RAKWireless/RAK10706-Signal-Meter/SignalMeterTool/assets/11-menu-info.png

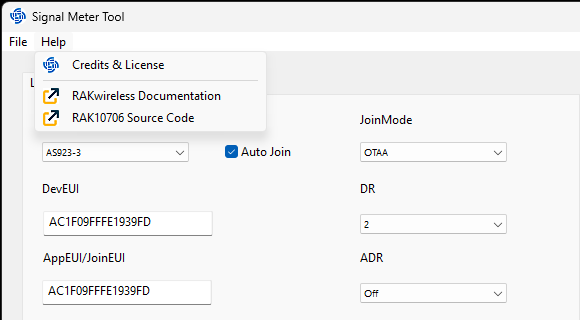
SignalMeterTool/assets/11-menu-info.png
