RAKWireless/RAK10706-Signal-Meter/sd-card.cpp

/**
 * @file sd-card.cpp
 * @author Bernd Giesecke (bernd@giesecke.tk)
 * @brief SD card functions
 * @version 0.2
 * @date 2024-11-18
 *
 * @copyright Copyright (c) 2024
 *
 */
#include "app.h"
#include <SD.h> //http://librarymanager/All#SD

/** Forward declarations */
void dir_sd(File dir);
void dump_sd_file(const char *path);

/** Pointer to current log file */
File log_file;

/** Flag if write or file create failed */
volatile bool sd_card_error = false;

/** Number of lines written to file */
volatile uint16_t lines_written = 0;

/**
 * @brief Initialize SD card
 *
 * @return true SD card found
 * @return false no SD card found
 */
bool init_sd(void)
{
	digitalWrite(WB_IO2, HIGH);
	delay(50);

#if 0
	// For debug, get more info about SD card
	Sd2Card card;
	SdVolume volume;

	if (!card.init(SPI_QUARTER_SPEED, WB_SPI_CS)) // SPI_QUARTER_SPEED SPI_HALF_SPEED SPI_FULL_SPEED
	{
		MYLOG("SD", "Card Init Failed! Please make sure the card is inserted!");
		return false;
	}

	switch (card.type())
	{
	case SD_CARD_TYPE_SD1:
		MYLOG("SD", "Cardtype SD1");
		break;
	case SD_CARD_TYPE_SD2:
		MYLOG("SD", "Cardtype SD2");
		break;
	case SD_CARD_TYPE_SDHC:
		MYLOG("SD", "Cardtype SDHC");
		break;
	default:
		MYLOG("SD", "Cardtype inknown");
	}

	if (!volume.init(card))
	{
		MYLOG("SD", "Could not find FAT16/FAT32 partition.\nMake sure you've formatted the card");
		return false;
	}

	MYLOG("SD", "Clusters: %ld", volume.clusterCount());
	MYLOG("SD", "Blocks x Cluster: %d", volume.blocksPerCluster());

	MYLOG("SD", "Total Blocks: %ld", volume.blocksPerCluster() * volume.clusterCount());

	// print the type and size of the first FAT-type volume
	uint32_t volumesize;
	MYLOG("SD", "Volume type is:    FAT%d", volume.fatType(), DEC);

	volumesize = volume.blocksPerCluster(); // clusters are collections of blocks
	volumesize *= volume.clusterCount();	// we'll have a lot of clusters
	volumesize /= 2;						// SD card blocks are always 512 bytes (2 blocks are 1 KB)
	MYLOG("SD", "Volume size (KB): %ld", volumesize);
	MYLOG("SD", "Volume size (MB): %ld", volumesize / 1024);
	MYLOG("SD", "Volume size (GB): %.2f", (float)volumesize / 1024 / 1024.0);
#endif

	if (!SD.begin(WB_SPI_CS))
	{
		MYLOG("SD", "SD begin failed.\nMake sure you've formatted the card and it is inserted");
		return false;
	}

#if 0
	// For debug, list available files
	File dir_file = SD.open("/", FILE_WRITE);
	dir_sd(dir_file);
	dir_file.close();

	uint16_t file_num = 0;
	sprintf((char *)file_name, "%04d-log.csv", file_num);
	while (true)
	{
		if (SD.exists((const char *)file_name))
		{
			MYLOG("SD", "Content of %s:", file_name);
			dump_sd_file((const char *)file_name);
			file_num++;
			sprintf((char *)file_name, "%04d-log.csv", file_num);
		}
		else
		{
			break;
		}
	}
#endif

	SD.end();
	return true;
}

#if 0
/**
 * @brief Send directory of a folder to the Serial port
 *
 * @param dir
 */
void dir_sd(File dir)
{
	digitalWrite(WB_IO2, HIGH);
	delay(50);
	while (true)
	{

		log_file = dir.openNextFile();
		if (!log_file)
		{
			// no more files
			break;
		}
		Serial.print(log_file.name());
		if (log_file.isDirectory())
		{
			Serial.println("/");
			dir_sd(log_file);
		}
		else
		{
			// files have sizes, directories do not
			Serial.print("\t\t");
			Serial.println(log_file.size(), DEC);
		}
		log_file.close();
	}
}
#endif

/**
 * @brief Send content of all files to the Serial port
 *
 */
void dump_all_sd_files(void)
{
	SD.begin(WB_SPI_CS);
	uint16_t file_num = 0;
	sprintf((char *)file_name, "%04d-log.csv", file_num);
	while (true)
	{
		if (SD.exists((const char *)file_name))
		{
			// MYLOG("SD", "Content of %s:", file_name);
			// Serial.println("=====================================================");
			log_file = SD.open((const char *)file_name, FILE_READ); // re-open the file for reading.
			if (log_file)
			{
				oled_clear();
				oled_write_header("LOGGING", false);
				oled_add_line((char *)"Dumping SD card");
				oled_add_line((char *)"Do not power off");
				sprintf(line_str, "%s", file_name);
				oled_write_line(3, 0, line_str);
				oled_display();
				Serial.printf("%s\r\n", file_name);
				Serial.write(0x02);
				Serial.flush();
				// Delay to give receiver time to get filename
				delay(500);
				while (log_file.available())
				{
					Serial.write(log_file.read()); // read from the file until there's nothing else in it.
					delay(5);
				}
				log_file.close(); // close the file.
				Serial.flush();

				// Delay to give receiver time to get EOF marker
				delay(500);

				Serial.write(0x03);
				Serial.flush();

				// Delay to give receiver time to get EOF marker
				delay(500);
			}
			else
			{
				MYLOG("SD", "Failed to open file for reading."); // if the file didn't open, print an error.
			}

			file_num++;
			sprintf((char *)file_name, "%04d-log.csv", file_num);
			MYLOG("SD", "Look for next file %s", file_name);
		}
		else
		{
			Serial.write(0x17);
			Serial.flush();
			break;
		}
	}

	SD.end();
}

/**
 * @brief Send the content of a file to the Serial port
 *
 * @param path Path as string
 */
void dump_sd_file(const char *path)
{
	digitalWrite(WB_IO2, HIGH);
	delay(50);
	MYLOG("SD", "Reading file: %s", path);

	SD.begin(WB_SPI_CS);

	log_file = SD.open(path, FILE_READ); // re-open the file for reading.
	if (log_file)
	{
		while (log_file.available())
		{
			Serial.write(log_file.read()); // read from the file until there's nothing else in it.
			delay(5);
		}
		log_file.close(); // close the file.
	}
	else
	{
		MYLOG("SD", "Failed to open file for reading."); // if the file didn't open, print an error.
	}
	SD.end();
}

/**
 * @brief Erase all files on the SD card
 *
 */
void clear_sd_file(void)
{
	digitalWrite(WB_IO2, HIGH);
	delay(50);

	// Just to be sure
	SD.end();

	SD.begin(WB_SPI_CS);

	File dir = SD.open("/", FILE_READ);
	if (dir)
	{
		while (true)
		{
			log_file = dir.openNextFile();
			if (!log_file)
			{
				// no more files
				MYLOG("SD", "No more files");
				break;
			}
			if (!log_file.isDirectory())
			{
				char *last_file_name = log_file.name();
				SD.remove((const char *)last_file_name);
			}
			log_file.close();
		}
		dir.close();
	}
	else
	{
		MYLOG("SD", "Can't open root");
	}
	SD.end();
}

/**
 * @brief Create a new file on the SD card.
 * 		Checks available files and generates a new file name
 *
 * @return true File created
 * @return false File could not be created
 */
bool create_sd_file(void)
{
	digitalWrite(WB_IO2, HIGH);
	delay(50);

	SD.begin(WB_SPI_CS);

	File dir = SD.open("/", FILE_READ);
	uint16_t file_num = 0;
	sprintf((char *)file_name, "%04d-log.csv", file_num);
	if (dir)
	{
		while (true)
		{
			log_file = dir.openNextFile();
			if (!log_file)
			{
				// no more files
				MYLOG("SD", "New filename = %s", file_name);
				break;
			}
			if (!log_file.isDirectory())
			{
				char *last_file_name = log_file.name();
				std::string file_string = last_file_name;
				if (file_string.find("-LOG.CSV") != string::npos)
				{
					bool valid_file = true;
					for (int idx = 0; idx < 4; idx++)
					{
						if ((last_file_name[idx] < '0') || (last_file_name[idx] > '9'))
						{
							valid_file = false;
						}
					}
					if (valid_file)
					{
						MYLOG("SD", "Found logfile %s", last_file_name);
						last_file_name[4] = 0x00;
						file_num = atol(last_file_name);
						sprintf((char *)file_name, "%04d-LOG.CSV", file_num + 1);
						MYLOG("SD", "Next file is %s", file_name);
					}
					else
					{
						MYLOG("SD", "Not a log file %s", last_file_name);
					}
				}
				else
				{
					MYLOG("SD", "Not a log file %s", last_file_name);
				}
			}
			log_file.close();
		}
		dir.close();
	}
	else
	{
		MYLOG("SD", "Can't open root");
	}

	log_file = SD.open((const char *)file_name, FILE_WRITE);
	if (log_file)
	{
		MYLOG("SD", "Writing Header to %s", file_name);
		if (g_custom_parameters.test_mode == MODE_LINKCHECK)
		{
			if (g_custom_parameters.location_on)
			{
				log_file.println("\"time\";\"Mode\";\"Gw\";\"Lat\";\"Lng\";\"RX RSSI\";\"RX SNR\";\"Demod\";\"TX DR\";\"Lost\"");
			}
			else
			{
				log_file.println("\"time\";\"Mode\";\"Gw\";\"RX RSSI\";\"RX SNR\";\"Demod\";\"TX DR\";\"Lost\"");
			}
		}
		else if (g_custom_parameters.test_mode == MODE_FIELDTESTER)
		{
			log_file.println("\"time\";\"Mode\";\"Gw\";\"Lat\";\"Lng\";\"min RSSI\";\"max RSSI\";\"RX RSSI\";\"RX SNR\";\"min Dist\";\"max Dist\";\"TX DR\";\"Lost\"");
		}
		else if (g_custom_parameters.test_mode == MODE_FIELDTESTER_V2)
		{
			log_file.println("\"time\";\"Mode\";\"Gw\";\"Lat\";\"Lng\";\"max RSSI\";\"max SNR\";\"RX RSSI\";\"RX SNR\";\"min Dist\";\"max Dist\";\"TX DR\";\"PLR\"");
		}
		else // P2P mode
		{
			if (g_custom_parameters.location_on)
			{
				log_file.println("\"time\";\"Mode\";\"Lat\";\"Lng\";\"RX RSSI\";\"RX SNR\"");
			}
			else
			{
				log_file.println("\"time\";\"Mode\";\"RX RSSI\";\"RX SNR\"");
			}
		}
		log_file.flush();
		log_file.close();
		SD.end();
		sd_card_error = false;
		return true;
	}
	else
	{
		// Error creating file. Card might be full?
		sd_card_error = true;
	}
	SD.end();

	return false;
}

/**
 * @brief Write to the current log file
 *
 */
void write_sd_entry(void)
{

	digitalWrite(WB_IO2, HIGH);
	delay(50);

	SD.begin(WB_SPI_CS);

	char line_entry[512];
	if (!SD.exists((const char *)file_name))
	{
		MYLOG("SD", "Can't find %s", file_name);
	}
	else
	{
		MYLOG("SD", "Found %s", file_name);
	}

	log_file = SD.open((const char *)file_name, FILE_WRITE);
	if (log_file)
	{
		sd_card_error = false;
		size_t bytes_to_write = 0;
		if (g_custom_parameters.test_mode == MODE_LINKCHECK)
		{
			if (g_custom_parameters.location_on)
			{
				// log_file.println("\"time\";\"Mode\";\"Gw\";\"Lat\";\"Lng\";\"RX RSSI\";\"RX SNR\";\"Demod\";\"TX DR\";\"Lost\"");
				bytes_to_write = snprintf(line_entry, 511, "%04d-%02d-%02d %02d:%02d:%02d;%d;%d;%.6f;%.6f;%d;%d;%d;%d;%d",
										  result.year, result.month, result.day, result.hour, result.min, result.sec,
										  result.mode, result.gw,
										  result.lat, result.lng,
										  result.rx_rssi,
										  result.rx_snr,
										  result.demod, result.tx_dr, result.lost);
			}
			else
			{
				// log_file.println("\"time\";\"Mode\";\"Gw\";\"RX RSSI\";\"RX SNR\";\"Demod\";\"TX DR\";\"Lost\"");
				bytes_to_write = snprintf(line_entry, 511, "%04d-%02d-%02d %02d:%02d:%02d;%d;%d;%d;%d;%d;%d;%d",
										  result.year, result.month, result.day, result.hour, result.min, result.sec,
										  result.mode, result.gw,
										  result.rx_rssi,
										  result.rx_snr,
										  result.demod, result.tx_dr, result.lost);
			}
		}
		else if (g_custom_parameters.test_mode == MODE_FIELDTESTER)
		{
			// log_file.println("\"time\";\"Mode\";\"Gw\";\"Lat\";\"Lng\";\"min RSSI\";\"max RSSI\";\"RX RSSI\";\"RX SNR\";\"min Dist\";\"max Dist\";\"TX DR\";\"Lost\"");
			bytes_to_write = snprintf(line_entry, 511, "%04d-%02d-%02d %02d:%02d:%02d;%d;%d;%.6f;%.6f;%d;%d;%d;%d;%d;%d;%d;%d",
									  result.year, result.month, result.day, result.hour, result.min, result.sec,
									  result.mode, result.gw,
									  result.lat, result.lng,
									  result.min_rssi, result.max_rssi, result.rx_rssi,
									  result.rx_snr,
									  result.min_dst, result.max_dst, result.tx_dr, result.lost);
		}
		else if (g_custom_parameters.test_mode == MODE_FIELDTESTER_V2)
		{
			// log_file.println("\"time\";\"Mode\";\"Gw\";\"Lat\";\"Lng\";\"max RSSI\";\"max SNR\";\"RX RSSI\";\"RX SNR\";\"min Dist\";\"max Dist\";\"TX DR\";\"PLR\"");
			bytes_to_write = snprintf(line_entry, 511, "%04d-%02d-%02d %02d:%02d:%02d;%d;%d;%.6f;%.6f;%d;%d;%d;%d;%d;%d;%d;%.1f",
									  result.year, result.month, result.day, result.hour, result.min, result.sec,
									  result.mode, result.gw,
									  result.lat, result.lng,
									  result.max_rssi, result.max_snr, result.rx_rssi,
									  result.rx_snr,
									  result.min_dst, result.max_dst, result.tx_dr, (float)result.lost / 10.0f);
		}
		else // LoRa P2P
		{
			if (g_custom_parameters.location_on)
			{
				// log_file.println("\"time\";\"Mode\";\"Lat\";\"Lng\";\"RX RSSI\";\"RX SNR\"");
				bytes_to_write = snprintf(line_entry, 511, "%04d-%02d-%02d %02d:%02d:%02d;%d;%.6f;%.6f;%d;%d",
										  result.year, result.month, result.day, result.hour, result.min, result.sec,
										  result.mode,
										  result.lat, result.lng,
										  result.rx_rssi,
										  result.rx_snr);
			}
			else
			{
				// log_file.println("\"time\";\"Mode\";\"RX RSSI\";\"RX SNR\"");
				bytes_to_write = snprintf(line_entry, 511, "%04d-%02d-%02d %02d:%02d:%02d;%d;%d;%d",
										  result.year, result.month, result.day, result.hour, result.min, result.sec,
										  result.mode,
										  result.rx_rssi,
										  result.rx_snr);
			}
		}

		MYLOG("SD", "Writing:\r\n%s", line_entry);
		size_t written = log_file.println(line_entry);
		if (written != bytes_to_write + 2) // Including /r/n
		{
			MYLOG("SD", "Written: %d expected %d", written, bytes_to_write);
			// Error writing to file. Card might be full?
			sd_card_error = true;
		}
		else
		{
			sd_card_error = false;
		}
		log_file.flush();
		log_file.close();

		lines_written++;
	}
	else
	{
		// Error writing to file. Card might be full?
		sd_card_error = true;
		MYLOG("SD", "Error writing to %s", file_name);
	}

	SD.end();

	if (lines_written == 300)
	{
		sd_card_error = create_sd_file();
		lines_written = 0;
	}

	ready_to_dump = true;

	return;
}
